Markuselectronics/DIY-USB-C-Reflow-Hotplate/Firmware/UserCode/SI_Units.h

#ifndef SI_Units_h
	#define SI_Units_h
	
	static constexpr float sec = 1;
	static constexpr float ms = 1e-3*sec;
	static constexpr float us = 1e-6*sec;
	static constexpr float min = 60*sec;
	static constexpr float hour = 60 * 60 * min;
	static constexpr float day = 60*60*24*sec;
	
	
	
#endif
